YaePak/DESIGN-AND-IMPLEMENTATION-OF-AN-ESP32-S3-BASED-3D-SCANNING-SYSTEM/3D-printed frame/Side_View.png

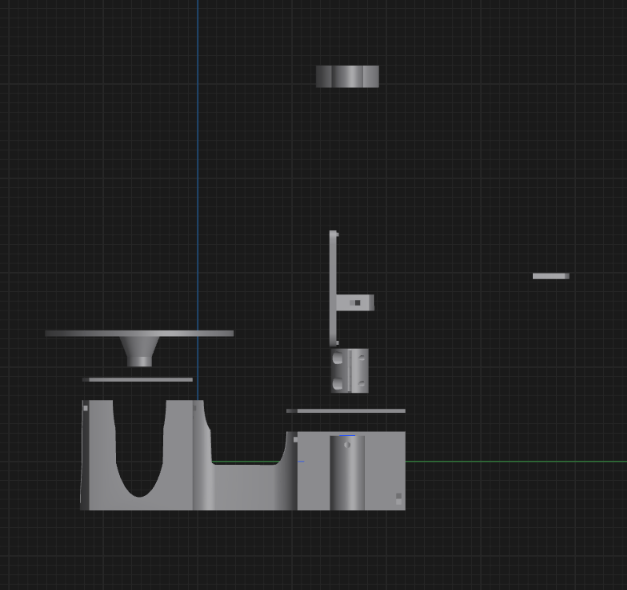
3D-printed frame/Side_View.png
